slacky1965/smoke_sensor_zed/doc/images/z2m_about.jpg

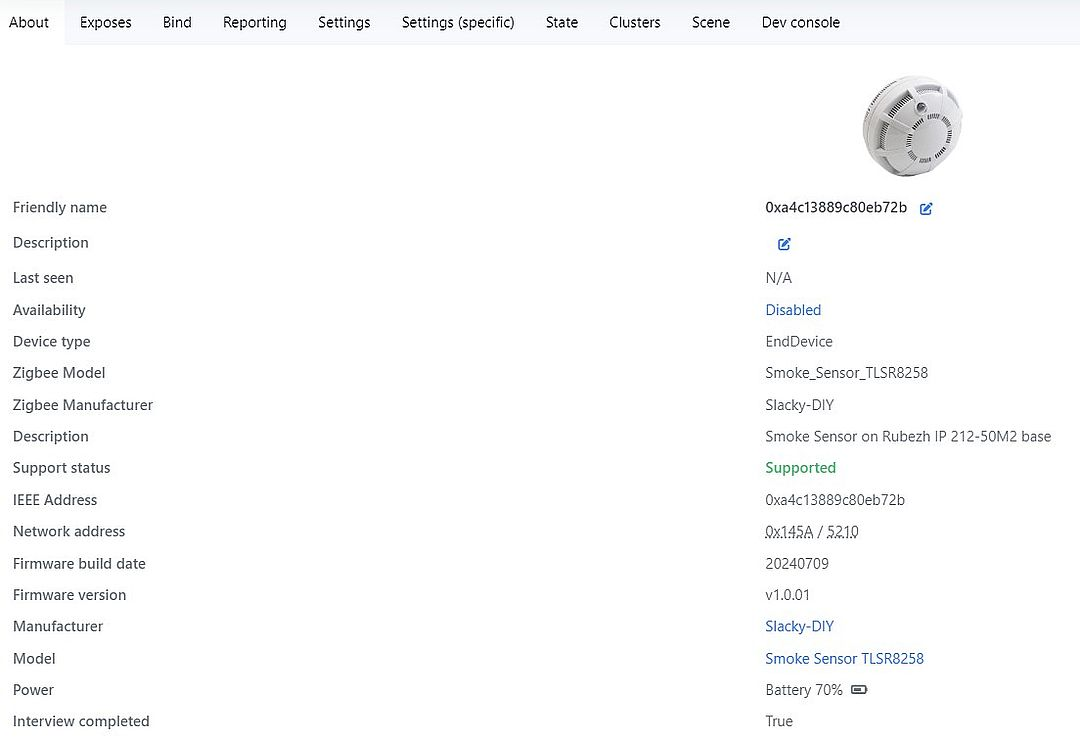
doc/images/z2m_about.jpg
