slacky1965/smoke_sensor_zed/tl_zigbee_sdk/platform/chip_b91/usbhw.h

/********************************************************************************************************
 * @file    usbhw.h
 *
 * @brief   This is the header file for B91
 *
 * @author  Driver Group
 * @date    2019
 *
 * @par     Copyright (c) 2019, Telink Semiconductor (Shanghai) Co., Ltd. ("TELINK")
 *
 *          Licensed under the Apache License, Version 2.0 (the "License");
 *          you may not use this file except in compliance with the License.
 *          You may obtain a copy of the License at
 *
 *              http://www.apache.org/licenses/LICENSE-2.0
 *
 *          Unless required by applicable law or agreed to in writing, software
 *          distributed under the License is distributed on an "AS IS" BASIS,
 *          WITHOUT WARRANTIES OR CONDITIONS OF ANY KIND, either express or implied.
 *          See the License for the specific language governing permissions and
 *          limitations under the License.
 *
 *******************************************************************************************************/
/**	@page USBHW
 *
 *	Introduction
 *	===============
 *	USB hard ware .
 *
 *	API Reference
 *	===============
 *	Header File: usbhw.h
 */

#pragma once

#include "reg_include/register.h"
#include "analog.h"
#include "gpio.h"

typedef enum
{
	USB_IRQ_RESET_MASK   =BIT(0),
	USB_IRQ_250US_MASK   =BIT(1),
	USB_IRQ_SUSPEND_MASK =BIT(2),
}usb_irq_mask_e;

typedef enum
{
	USB_IRQ_RESET_STATUS   =BIT(5),
	USB_IRQ_250US_STATUS   =BIT(6),
	USB_IRQ_SUSPEND_STATUS =BIT(7),
}usb_irq_status_e;

typedef enum {
    USB_EDP8_IN         = 8,
    USB_EDP1_IN         = 1,
    USB_EDP2_IN         = 2,
    USB_EDP3_IN         = 3,
    USB_EDP4_IN         = 4,
    USB_EDP5_OUT        = 5,
    USB_EDP6_OUT        = 6,
    USB_EDP7_IN         = 7,
	USB_EDP_PRINTER_IN = 8,     // default hw buf len = 64
	USB_EDP_MOUSE = 2,			// default hw buf len = 8
	USB_EDP_KEYBOARD_IN = 1,	// default hw buf len = 8
	USB_EDP_IN = 3,				// default hw buf len = 16
	USB_EDP_AUDIO_IN = 4,		// default hw buf len = 64
	USB_EDP_PRINTER_OUT = 5,	// default hw buf len = 64
	USB_EDP_SPEAKER = 6,		// default hw buf len = 16
	USB_EDP_MIC = 7,			// default hw buf len = 16
	USB_EDP_MS_IN = 4,		// mass storage
	USB_EDP_MS_OUT = 5,
	USB_EDP_SOMATIC_IN = USB_EDP_AUDIO_IN,		//  when USB_SOMATIC_ENABLE, USB_EDP_PRINTER_OUT disable
	USB_EDP_SOMATIC_OUT = USB_EDP_PRINTER_OUT,
    USB_EDP_CDC_IN = 4,
    USB_EDP_CDC_OUT = 5,
}usb_ep_index;

// #defined in the standard spec
enum {
	USB_HID_AUDIO       	= 2,
	USB_HID_MOUSE       	= 1,
	USB_HID_KB_MEDIA    	= 3,// media
	USB_HID_KB_SYS      	= 4,// system : power,sleep,wakeup
	USB_HID_SOMATIC			= 5,// somatic sensor,  may have many report ids
};

/**
 * @brief     This function servers to set ed8 to fifo mode.
 * @return    none.
 */
static inline void usbhw_set_ep8_fifo_mode(void) {
	BM_SET(reg_usb_ep8_fifo_mode,FLD_USB_ENP8_FIFO_MODE);
}

/**
 * @brief     This function servers to reset the pointer of control Endpoint.
 * @return    none.
 */
static inline void usbhw_reset_ctrl_ep_ptr(void) {
	reg_ctrl_ep_ptr = 0;
}

/**
 * @brief     This function servers to get the irq status of control Endpoint.
 * @return    none.
 */
static inline unsigned int usbhw_get_ctrl_ep_irq(void) {
	return reg_ctrl_ep_irq_sta;
}

/**
 * @brief     This function servers to clear the irq status of control Endpoint.
 * @param[in] ep - selected  the Endpoint
 * @return    none.
 */
static inline void usbhw_clr_ctrl_ep_irq(int ep) {
#ifdef WIN32
	BM_CLR(reg_ctrl_ep_irq_sta, ep);
#else
	reg_ctrl_ep_irq_sta = ep;
#endif
}

/**
 * @brief     This function servers to set the value of control Endpoint.
 * @param[in] data - the value of control Endpoint
 * @return    none.
 */
static inline void usbhw_write_ctrl_ep_ctrl(unsigned char data) {
	reg_ctrl_ep_ctrl = data;
}

/**
 * @brief     This function servers to read the data of control Endpoint.
 * @return    the value of control Endpoint data
 */
static inline unsigned char usbhw_read_ctrl_ep_data(void) {
	return reg_ctrl_ep_dat;
}

/**
 * @brief     This function servers to write the data of control Endpoint.
 * @param[in] data -  the data of control Endpoint to write
 * @return    none
 */
static inline void usbhw_write_ctrl_ep_data(unsigned char data) {
	reg_ctrl_ep_dat = data;
}

/**
 * @brief     This function servers to determine whether control Endpoint is busy.
 * @return    1: busy; 0: not busy.
 */
static inline int usbhw_is_ctrl_ep_busy(void) {
	return reg_ctrl_ep_irq_sta & FLD_USB_EP_BUSY;
}


/**
 * @brief     This function servers to reset the pointer of Endpoint.
 * @param[in] ep - select the Endpoint
 * @return    none.
 */
static inline void usbhw_reset_ep_ptr(unsigned int ep) {
	reg_usb_ep_ptr(ep) = 0;
}


/**
 * @brief     This function servers to set the buffer address of data endpoint.
 * @param[in] ep - select the data endpoint.
 * @param[in] addr - data endpoint buffer address.
 * @return    none.
 */
static inline void usbhw_set_ep_addr(usb_ep_index ep, unsigned char addr)
{
    reg_usb_ep_buf_addr(ep) = addr & 0xff;
}

/**
 * @brief     This function servers to set the irq mask of Endpoint.
 * @return    none.
 */
static inline void usbhw_set_eps_irq_mask(usb_ep_irq_e mask)
{
	reg_usb_ep_irq_mask|=mask;

}

/**
 * @brief     This function servers to clr the irq mask of Endpoint.
 * @return    none.
 */
static inline void usbhw_clr_eps_irq_mask(usb_ep_irq_e mask)
{
	reg_usb_ep_irq_mask &=(~mask);

}

/**
 * @brief     This function servers to get the irq status of Endpoint.
 * @return    none.
 */
static inline unsigned int usbhw_get_eps_irq(void) {
	return reg_usb_ep_irq_status;
}

/**
 * @brief     This function servers to clear the irq status of Endpoint.
 * @param[in] ep - selected  the Endpoint
 * @return    none.
 */
static inline void usbhw_clr_eps_irq(int ep) {
	reg_usb_ep_irq_status = ep;
}

/**
 * @brief     This function servers to set usb irq mask.
 * @param[in]  mask -the  irq mask of usb.
 * @return    none.
 */
static inline void usbhw_set_irq_mask( usb_irq_mask_e mask)
{
	reg_usb_irq_mask|=mask;
}

/**
 * @brief     This function servers to clr usb irq mask.
 * @param[in]  mask -the  irq mask of usb.
 * @return    none.
 */
static inline void usbhw_clr_irq_mask( usb_irq_mask_e mask)
{
	reg_usb_irq_mask &= (~mask);
}

/**
 * @brief     This function servers to get usb irq status.
 * @param[in]  status -the  irq status of usb.
 * @retval	  non-zero   -  the interrupt occurred.
 * @retval	  zero  -  the interrupt did not occur.
 */
static inline unsigned char  usbhw_get_irq_status(usb_irq_status_e status)
{
	return reg_usb_irq_mask&status;
}

/**
 * @brief     This function servers to clr usb irq status.
 * @param[in]  status -the  irq status of usb.
 * @return    none.
 */
static inline void usbhw_clr_irq_status(usb_irq_status_e status)
{
    /** the reg_usb_irq_mask register mask and status are in the same register
     * enum
     * {
     *      FLD_USB_IRQ_RESET_MASK   = 	BIT(0),
     *      FLD_USB_IRQ_250US_MASK 	 = 	BIT(1),
     *      FLD_USB_IRQ_SUSPEND_MASK = 	BIT(2),
     *      FLD_USB_IRQ_RESET_LVL	 = 	BIT(3),
     *      FLD_USB_IRQ_250US_LVL	 = 	BIT(4),
     *      FLD_USB_IRQ_RESET_O 	 = 	BIT(5),
     *      FLD_USB_IRQ_250US_O		 = 	BIT(6),
     *      FLD_USB_IRQ_SUSPEND_O	 = 	BIT(7),
     * };
     * Flags can only be cleared with |=, not by direct assignment. */
	reg_usb_irq_mask|=status; 
}


/**
 * @brief     This function servers to enable Endpoint.
 * @param[in] ep - selected  the Endpoint
 * @return    none.
 */
static inline void  usbhw_set_eps_en(usb_ep_en_e ep)
{
	reg_usb_edp_en= ep;
}

/**
 * @brief     This function servers to enable Endpoint.
 * @param[in] ep - selected  the Endpoint
 * @return    none.
 */
static inline void  usbhw_set_eps_dis(usb_ep_en_e ep)
{
	reg_usb_edp_en &=(~ ep);
}

/**
 * @brief     This function servers to read the data of Endpoint.
 * @param[in] ep - selected the Endpoint
 * @return    the value of Endpoint
 */
static inline unsigned char usbhw_read_ep_data(unsigned int ep) {
	return reg_usb_ep_dat(ep);
}

/**
 * @brief     This function servers to write the data of Endpoint.
 * @param[in] ep   -  selected the Endpoint
 * @param[in] data -  the value of Endpoint
 * @return    none
 */
static inline void usbhw_write_ep_data(unsigned int ep, unsigned char data) {
	reg_usb_ep_dat(ep) = data;
}



/**
 * @brief     This function servers to enable the specified Endpoint.
 * @param[in] ep -  selected the Endpoint
 * @param[in] en -  1:enable,0:disable
 * @return    none
 */
static inline void usbhw_set_ep_en(unsigned int ep, unsigned char en) {
	if(en)
	{
		reg_usb_edp_en |= ep;
	}
	else
	{
		reg_usb_edp_en &= ~(ep);
	}
}

/**
 * @brief     This function servers to determine whether Endpoint is busy.
 * @param[in] ep -  selected the Endpoint
 * @return    1: busy; 0: not busy.
 */
static inline unsigned int usbhw_is_ep_busy(unsigned int ep) {
	return reg_usb_ep_ctrl(ep) & FLD_USB_EP_BUSY;
}

/**
 * @brief     This function servers to set the specified data EndPoint to ack.
 * @param[in] ep -  select the data EndPoint.
 * @return    none.
 */
static inline void usbhw_data_ep_ack(unsigned int ep) {
	reg_usb_ep_ctrl(ep) = FLD_USB_EP_BUSY;
}

/**
 * @brief     This function servers to set the specified data EndPoint to stall.
 * @param[in] ep -  select the data EndPoint.
 * @return    none.
 */
static inline void usbhw_data_ep_stall(unsigned int ep) {
	reg_usb_ep_ctrl(ep) = FLD_USB_EP_STALL;
}


/**
 * @brief     This function servers to set the threshold of printer.
 * @param[in] th - set the threshold for printer
 * @return    none.
 */
static inline void usbhw_set_printer_threshold(unsigned char th) {
	reg_usb_ep8_send_thres = th;
}

/**
 * @brief     This function servers to set in endpoint buffer max size(except 7 aiso mode).
 * @param[in] max_size - in endpoint max size.
 * @return    none.
 */
static inline void usbhw_set_eps_max_size(unsigned int max_size)
{
    reg_usb_ep_max_size = max_size >> 3;
}

/**
 * @brief      This function disables the manual interrupt
 *             (Endpoint8 is the alias of endpoint0)
 * @param[in]  m - the irq mode needs to set
 * @return     none
 */
void usbhw_disable_manual_interrupt(int m);

/**
 * @brief      This function enable the manual interrupt
 * @param[in]  m - the irq mode needs to set
 * @return     none
 */
void usbhw_enable_manual_interrupt(int m);

/**
 * @brief      This function sends a bulk of data to host via the specified endpoint
 * @param[in]  ep - the number of the endpoint
 * @param[in]  data - pointer to the data need to send
 * @param[in]  len - length in byte of the data need to send
 * @return     none
 */
void usbhw_write_ep(unsigned int ep, unsigned char * data, int len);

/**
 * @brief      This function sends two bytes data to host via the control endpoint
 *             (handy help function)
 * @param[in]  v - the two bytes data need to send
 * @return     none
 */
void usbhw_write_ctrl_ep_u16(unsigned short v);

/**
 * @brief   This function reads two bytes data from host via the control endpoint
 * @return  the two bytes data read from the control endpoint
 */
unsigned short usbhw_read_ctrl_ep_u16(void);

/**
 * @brief      This function enables or disables the internal pull-up resistor of DP pin of USB interface
 * @param[in]  en - enables or disables the internal pull-up resistor(1: enable 0: disable)
 * @return     none
 */
static inline void usb_dp_pullup_en (int en)
{
	unsigned char dat = analog_read_reg8(0x0b);
	if (en) {
		dat = dat | BIT(7);
	}
	else
	{
		dat = dat & 0x7f ;
	}

	analog_write_reg8 (0x0b, dat);
}

/**
 * @brief      This function serves to power on or down USB module
 * @param[in]  en - 1: power on 0: power down
 * @return     none
 */
static inline void usb_power_on(unsigned char en)
{
	if(en)
	{
		analog_write_reg8(0x7d,analog_read_reg8(0x7d)&0xfd);
	}
	else
	{
		analog_write_reg8(0x7d,analog_read_reg8(0x7d)|0x02);
	}
}

/**
 * @brief      This function serves to set GPIO MUX function as DP and DM pin of USB
 * @return     none.
 */
static inline void usb_set_pin_en(void)
{
	reg_gpio_func_mux(GPIO_PA5)=reg_gpio_func_mux(GPIO_PA5)&(~BIT_RNG(2,3));
	gpio_function_dis(GPIO_PA5);
	reg_gpio_func_mux(GPIO_PA6)=reg_gpio_func_mux(GPIO_PA6)&(~BIT_RNG(4,5));
	gpio_function_dis(GPIO_PA6);
	gpio_input_en(GPIO_PA5|GPIO_PA6);//DP/DM must set input enable
	usb_dp_pullup_en (1);
	write_reg8(0x100c01, (read_reg8(0x100c01) | BIT(7)));   //swire_usb_en
}
