slacky1965/smoke_sensor_zed/tl_zigbee_sdk/platform/services/b91m/plic_isr.c

/********************************************************************************************************
 * @file	plic_isr.c
 *
 * @brief	This is the source file for B91
 *
 * @author	Driver Group
 * @date	2019
 *
 * @par     Copyright (c) 2019, Telink Semiconductor (Shanghai) Co., Ltd. ("TELINK")
 *          All rights reserved.
 *
 *          Licensed under the Apache License, Version 2.0 (the "License");
 *          you may not use this file except in compliance with the License.
 *          You may obtain a copy of the License at
 *
 *              http://www.apache.org/licenses/LICENSE-2.0
 *
 *          Unless required by applicable law or agreed to in writing, software
 *          distributed under the License is distributed on an "AS IS" BASIS,
 *          WITHOUT WARRANTIES OR CONDITIONS OF ANY KIND, either express or implied.
 *          See the License for the specific language governing permissions and
 *          limitations under the License.
 *
 *******************************************************************************************************/
/*
 * All interrupt entry functions and weak definitions of related processing functions are defined here,If you dont use the relevant interrupt function,
 *  you can delete it to save ram_code space.
 ****************************************************************************************
 */
#include "tl_common.h"


volatile unsigned long mcause;
volatile unsigned long mepc;

/**
 * @brief  exception handler.this defines an exception handler to handle all the platform pre-defined exceptions.
 * @return none
 */
_attribute_ram_code_sec_ __attribute__((weak)) void except_handler()
{
	mcause = core_get_mcause();
	mepc   = core_get_mepc();
 	while(1){
 		/* Unhandled Trap */
 		for(volatile unsigned int i = 0; i < 0xffff; i++)
 		{
 			__asm__("nop");
 		}
 	}
}

_attribute_ram_code_sec_noinline_  __attribute__((weak)) void trap_entry(void) __attribute__ ((interrupt ("machine") , aligned(4)));
void trap_entry(void)
{
 	except_handler();
}

__attribute__((section(".ram_code"))) void default_irq_handler(void)
{
	
}


/**********************************************************************************
 * The interrupt sources used in the SDK.
 * If you want to use other interrupts, you'll need to find the corresponding registered 
 * function in the commented code below and put it here.
 **********************************************************************************/
void stimer_irq_handler(void) __attribute__((weak, alias("default_irq_handler")));
void uart0_irq_handler(void) __attribute__((weak, alias("default_irq_handler")));
void rf_irq_handler(void) __attribute__((weak, alias("default_irq_handler")));
void timer1_irq_handler(void) __attribute__((weak, alias("default_irq_handler")));
void timer0_irq_handler(void) __attribute__((weak, alias("default_irq_handler")));
void gpio_irq_handler(void) __attribute__((weak, alias("default_irq_handler")));
void gpio_risc0_irq_handler(void) __attribute__((weak, alias("default_irq_handler")));
void gpio_risc1_irq_handler(void) __attribute__((weak, alias("default_irq_handler")));
/**
 * @brief system timer interrupt handler.
 * @return none
 */
_attribute_ram_code_sec_noinline_ void entry_irq1(void) __attribute__ ((interrupt ("machine") , aligned(4)));
void entry_irq1(void)
{
	plic_isr(stimer_irq_handler,IRQ1_SYSTIMER);
}

/**
 * @brief uart0 interrupt handler.
 * @return none
 */
_attribute_ram_code_sec_noinline_ void entry_irq19(void) __attribute__ ((interrupt ("machine") , aligned(4)));
void entry_irq19(void)
{
	plic_isr(uart0_irq_handler,IRQ19_UART0);
}

/**
 * @brief telink rf interrupt handler.
 * @return none
 */
_attribute_ram_code_sec_noinline_ void entry_irq15(void) __attribute__ ((interrupt ("machine") , aligned(4)));
void entry_irq15(void)
{
	plic_isr(rf_irq_handler,IRQ15_ZB_RT);
}

/**
 * @brief timer1 interrupt handler.
 * @return none
 */
_attribute_ram_code_sec_noinline_ void entry_irq3(void) __attribute__ ((interrupt ("machine") , aligned(4)));
void entry_irq3(void)
{
	plic_isr(timer1_irq_handler,IRQ3_TIMER1);
}

/**
 * @brief timer0 interrupt handler.
 * @return none
 */
_attribute_ram_code_sec_noinline_ void entry_irq4(void) __attribute__ ((interrupt ("machine") , aligned(4)));
void entry_irq4(void)
{
	plic_isr(timer0_irq_handler,IRQ4_TIMER0);
}

/**
 * @brief gpio interrupt handler.
 * @return none
 */
_attribute_ram_code_sec_noinline_ void entry_irq25(void) __attribute__ ((interrupt ("machine") , aligned(4)));
void entry_irq25(void)
{
	plic_isr(gpio_irq_handler,IRQ25_GPIO);
}

/**
 * @brief gpio_risc0 interrupt handler.
 * @return none
 */
_attribute_ram_code_sec_noinline_ void entry_irq26(void) __attribute__ ((interrupt ("machine") , aligned(4)));
void entry_irq26(void)
{
	plic_isr(gpio_risc0_irq_handler,IRQ26_GPIO2RISC0);
}

/**
 * @brief gpio_risc1 interrupt handler.
 * @return none
 */
_attribute_ram_code_sec_noinline_ void entry_irq27(void) __attribute__ ((interrupt ("machine") , aligned(4)));
void entry_irq27(void)
{
	plic_isr(gpio_risc1_irq_handler,IRQ27_GPIO2RISC1);
}

#if 0
void stimer_irq_handler(void) __attribute__((weak, alias("default_irq_handler")));
void analog_irq_handler(void) __attribute__((weak, alias("default_irq_handler")));
void timer1_irq_handler(void) __attribute__((weak, alias("default_irq_handler")));
void timer0_irq_handler(void) __attribute__((weak, alias("default_irq_handler")));
void dma_irq_handler(void) __attribute__((weak, alias("default_irq_handler")));
void bmc_irq_handler(void) __attribute__((weak, alias("default_irq_handler")));
void usb_ctrl_ep_setup_irq_handler(void) __attribute__((weak, alias("default_irq_handler")));
void usb_ctrl_ep_data_irq_handler(void) __attribute__((weak, alias("default_irq_handler")));
void usb_ctrl_ep_status_irq_handler(void)  __attribute__((weak, alias("default_irq_handler")));
void usb_ctrl_ep_setinf_irq_handler(void) __attribute__((weak, alias("default_irq_handler")));
void usb_endpoint_irq_handler(void) __attribute__((weak, alias("default_irq_handler")));
void rf_dm_irq_handler(void) __attribute__((weak, alias("default_irq_handler")));
void rf_ble_irq_handler(void) __attribute__((weak, alias("default_irq_handler")));
void rf_bt_irq_handler(void) __attribute__((weak, alias("default_irq_handler")));
void rf_irq_handler(void) __attribute__((weak, alias("default_irq_handler")));

void pwm_irq_handler(void) __attribute__((weak, alias("default_irq_handler")));
void pke_irq_handler(void) __attribute__((weak, alias("default_irq_handler")));
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
{
	plic_isr(pm_irq_handler,IRQ62_PM_TM);
}

/**
 * @brief eoc interrupt handler.
 * @return none
 */
_attribute_ram_code_sec_noinline_ void entry_irq63(void) __attribute__ ((interrupt ("machine") , aligned(4)));
void entry_irq63(void)
{
	plic_isr(eoc_irq_handler,IRQ63_EOC);
}
#endif
